hza2002/owl/doc/assets/circuit-1.jpg

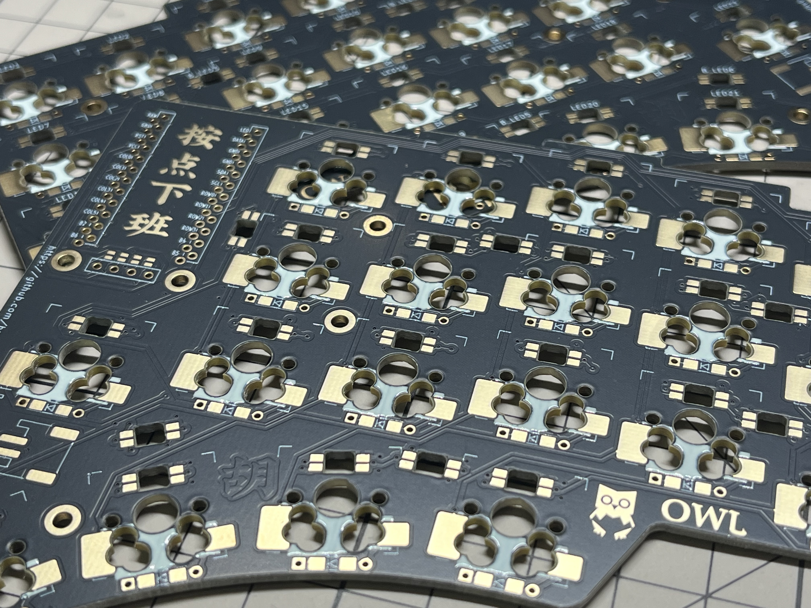
doc/assets/circuit-1.jpg
