hza2002/owl/doc/assets/circuit-2.jpg

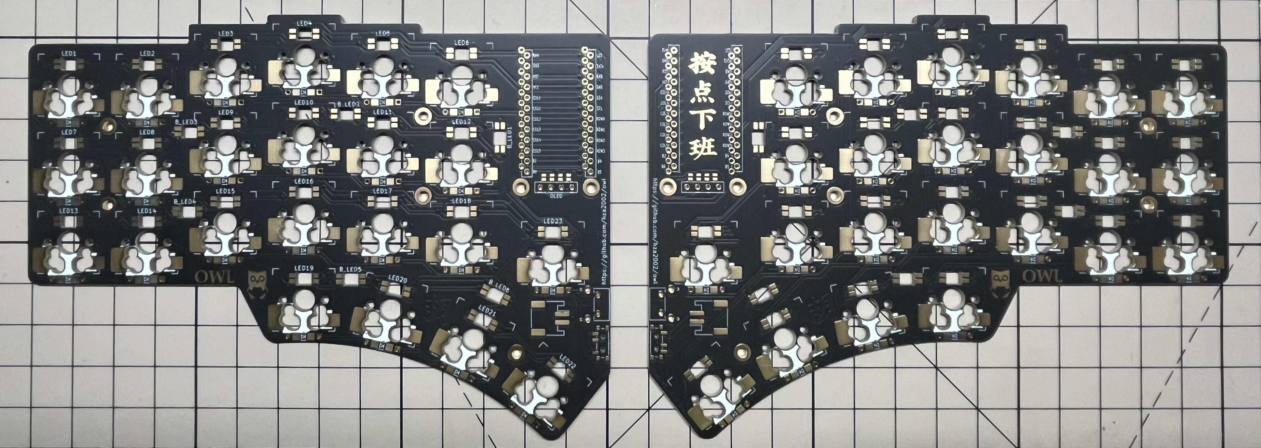
doc/assets/circuit-2.jpg
