hza2002/owl/doc/assets/jade.jpg

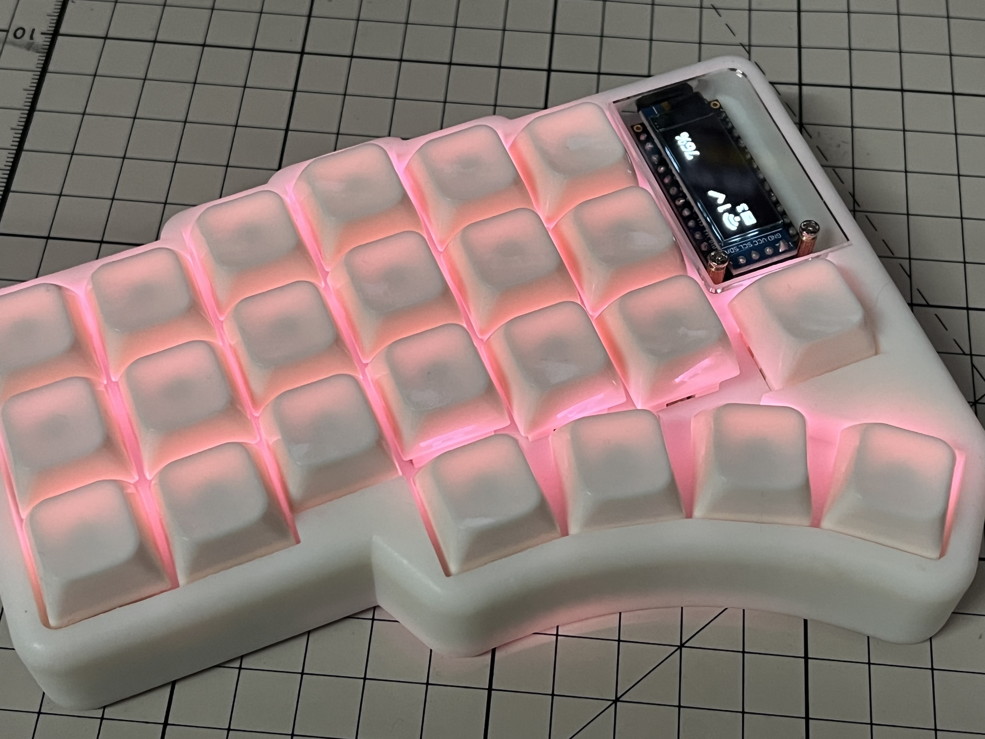
doc/assets/jade.jpg
