hza2002/owl/doc/assets/kailh choc.jpg

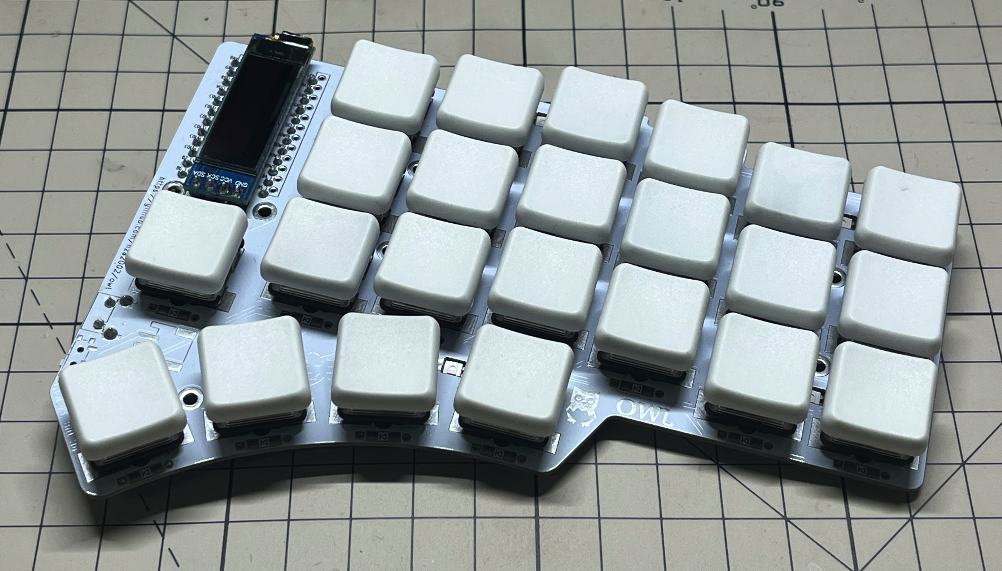
doc/assets/kailh choc.jpg
