hza2002/owl/doc/assets/keyless-1.jpg

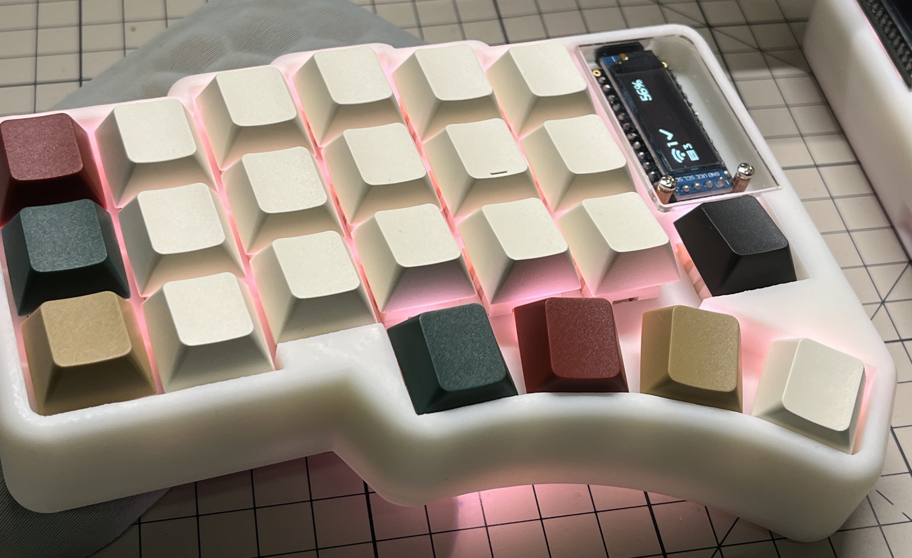
doc/assets/keyless-1.jpg
