hza2002/owl/doc/assets/keyless-2.jpg

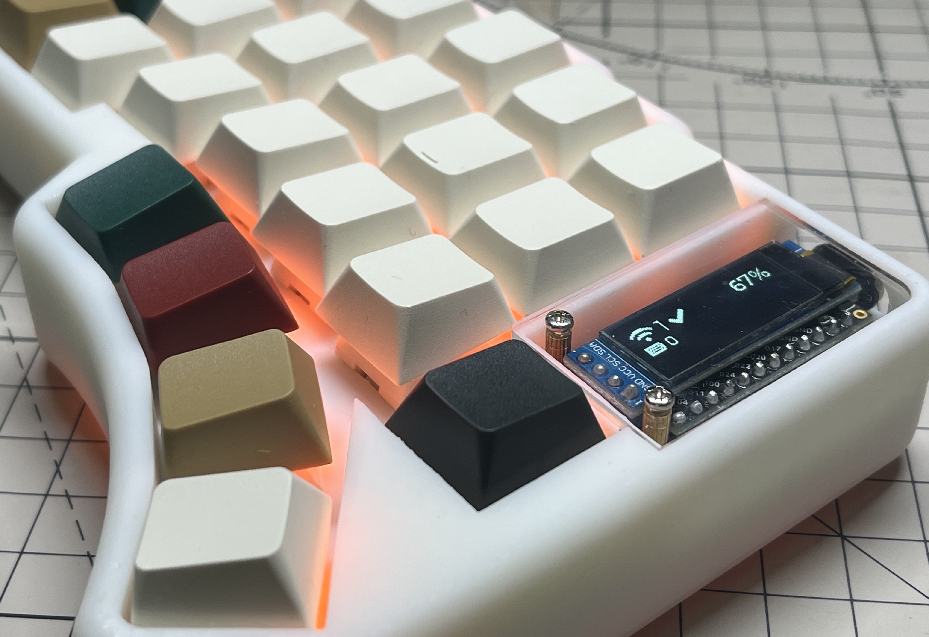
doc/assets/keyless-2.jpg
