hza2002/owl/doc/assets/RGB.jpg

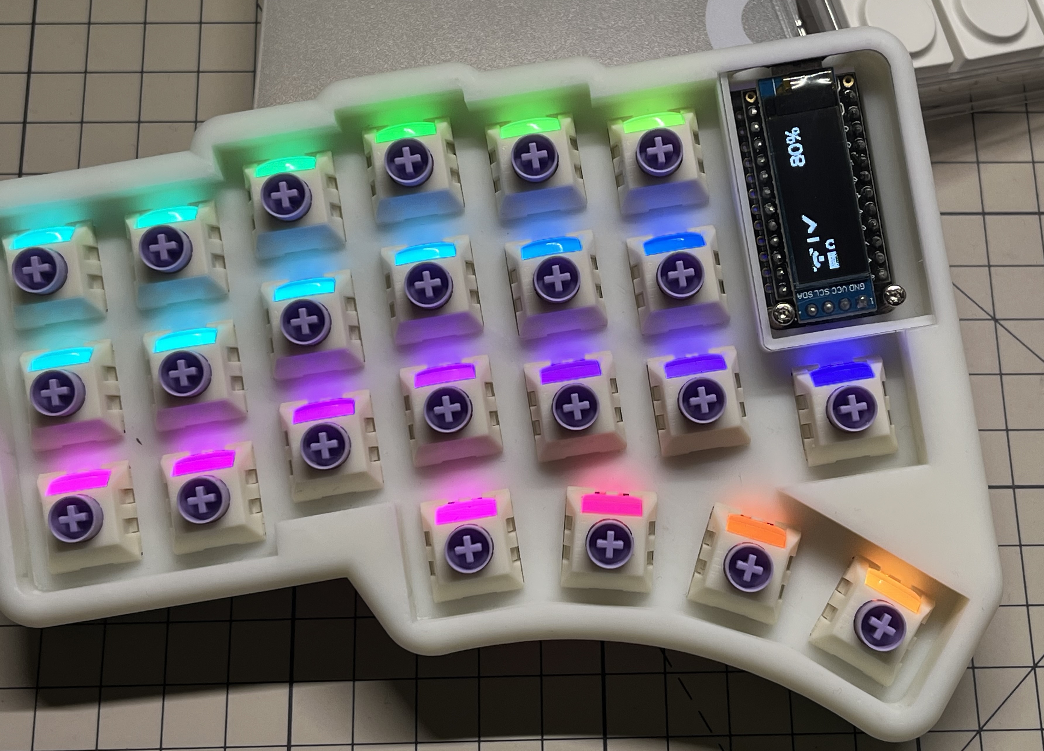
doc/assets/RGB.jpg
