hza2002/owl/doc/assets/toy-1.jpg

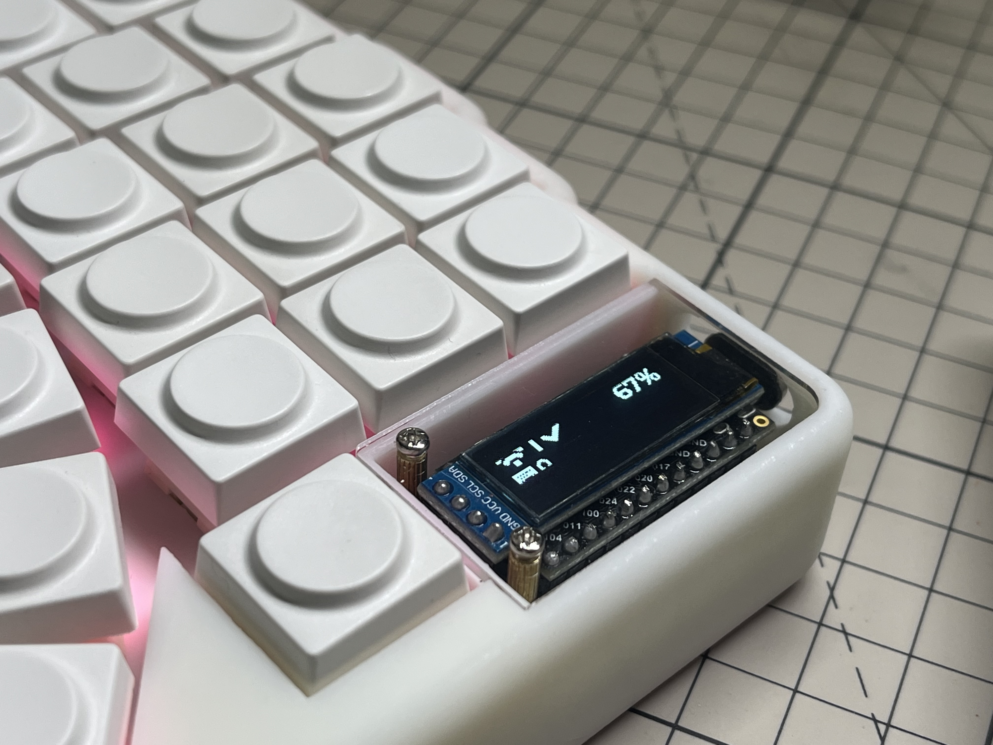
doc/assets/toy-1.jpg
