hza2002/owl/doc/assets/toy-2.jpg

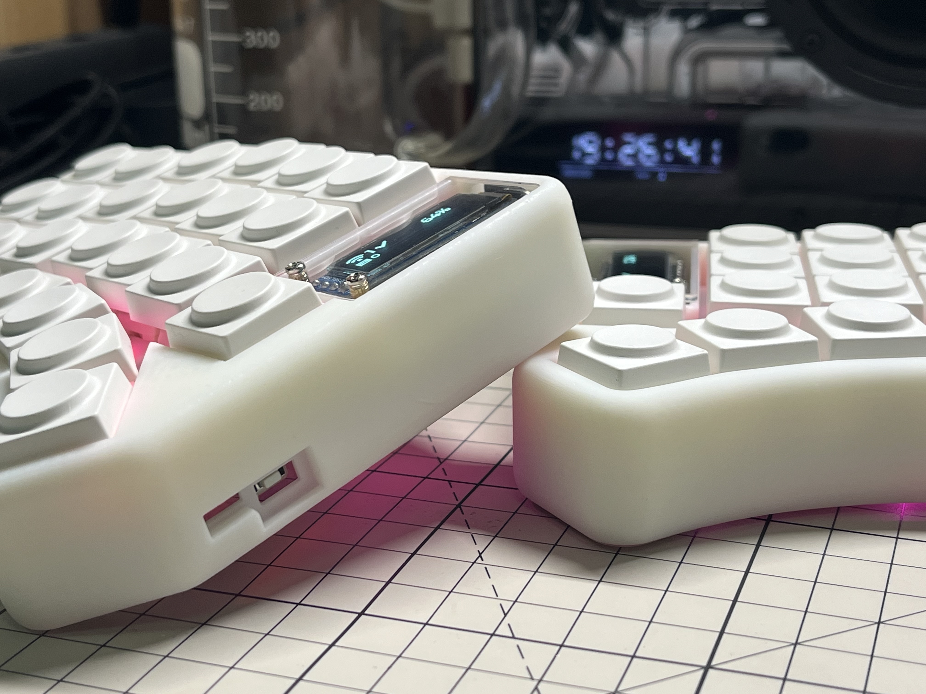
doc/assets/toy-2.jpg
