hza2002/owl/doc/assets/toy-3.jpg

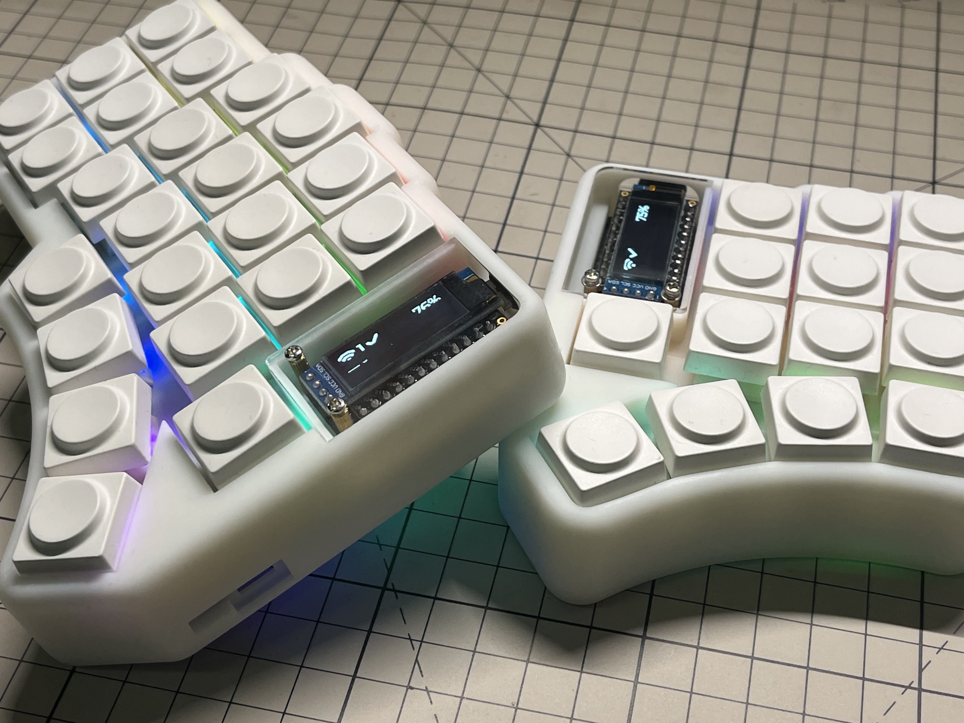
doc/assets/toy-3.jpg
