hza2002/owl/doc/assets/trans-1.jpg

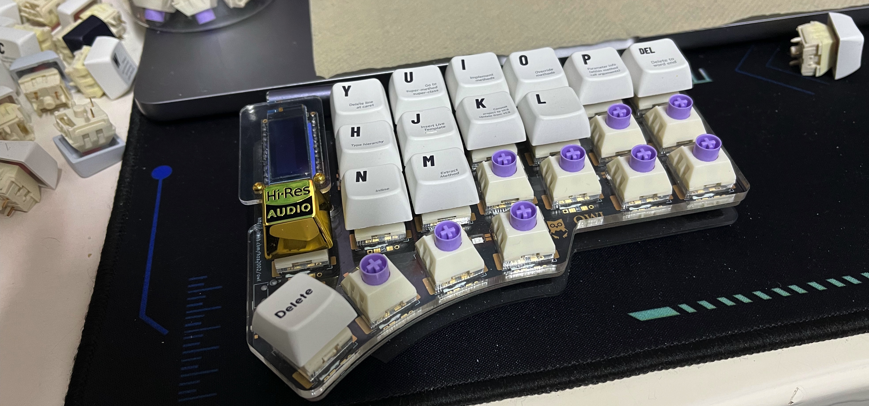
doc/assets/trans-1.jpg
