hza2002/owl/doc/assets/trans-2.jpg

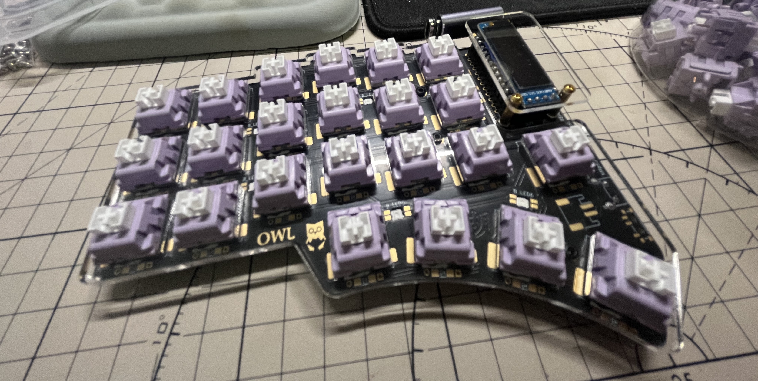
doc/assets/trans-2.jpg
