hza2002/owl/doc/assets/trans-3.jpg

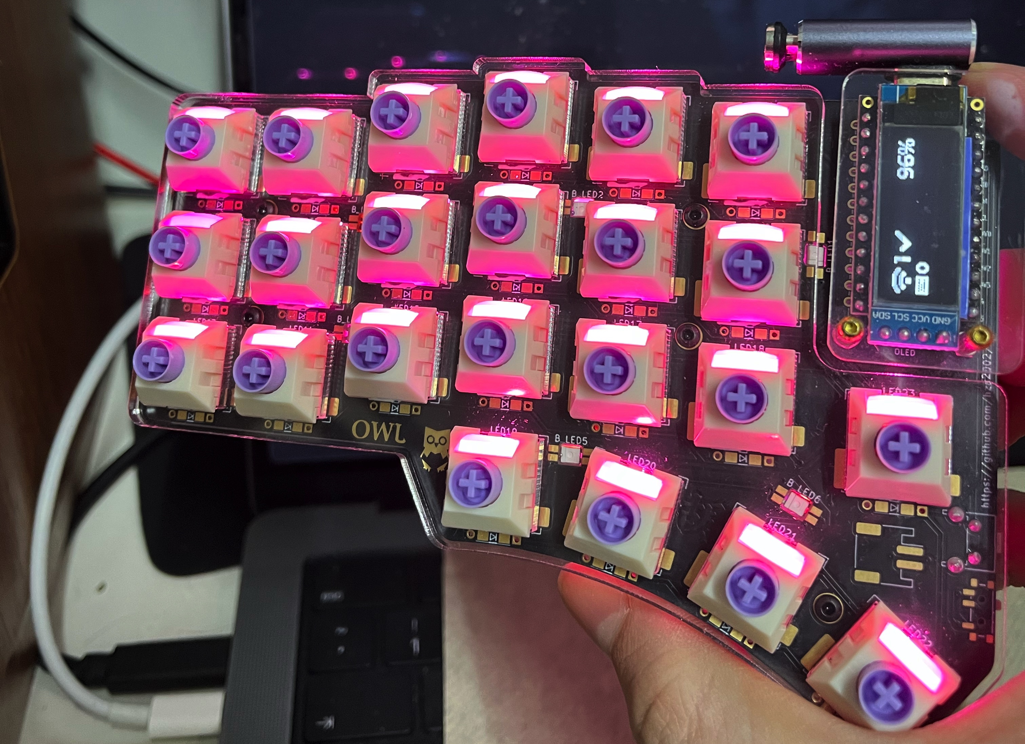
doc/assets/trans-3.jpg
